aaronlubinsky/Romi_Lubinsky_Guinnane/images/diagrams/romi_dim_param.png

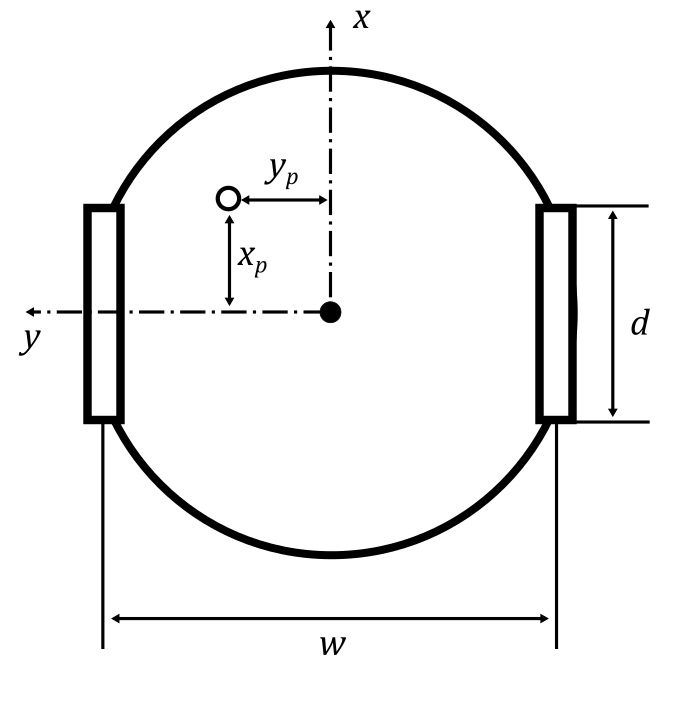
images/diagrams/romi_dim_param.png
