aaronlubinsky/Romi_Lubinsky_Guinnane/images/renders/RomiTop.jpg

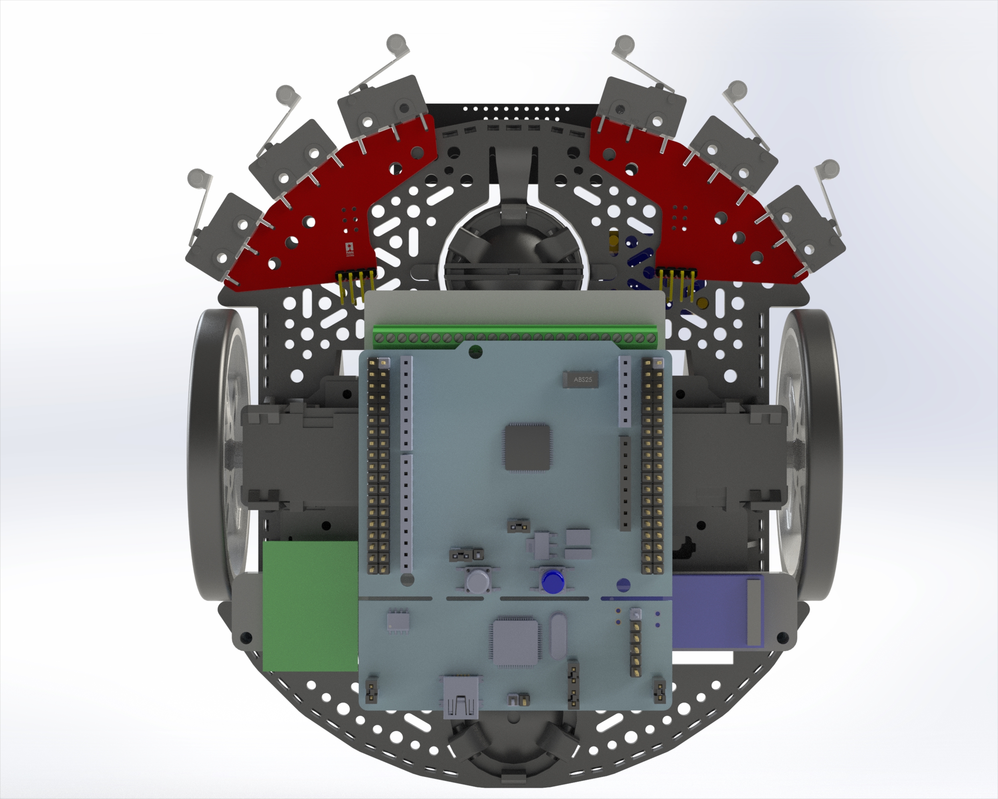
images/renders/RomiTop.jpg
