aaronlubinsky/Romi_Lubinsky_Guinnane/images/romi_pics/romi_back.jpg

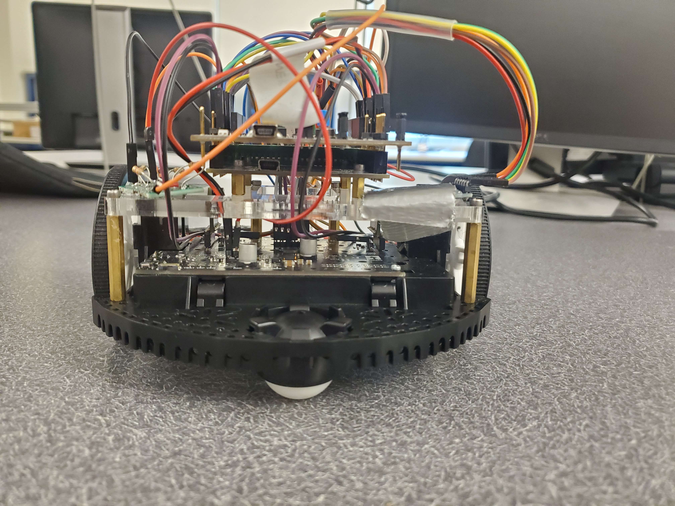
images/romi_pics/romi_back.jpg
