aaronlubinsky/Romi_Lubinsky_Guinnane/images/romi_pics/romi_bottom.jpg

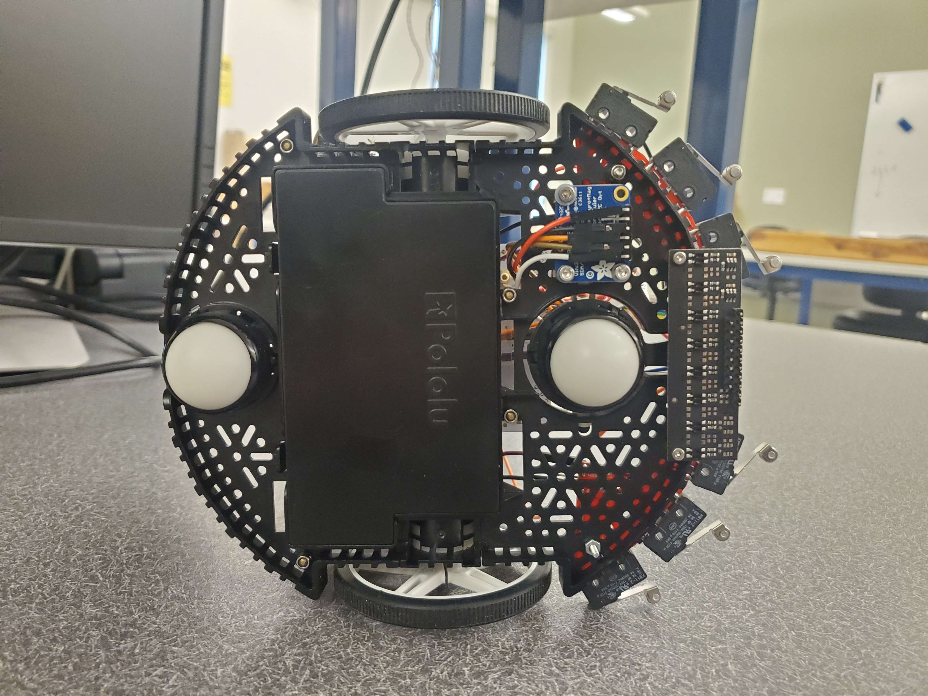
images/romi_pics/romi_bottom.jpg
