aaronlubinsky/Romi_Lubinsky_Guinnane/images/romi_pics/romi_top.jpg

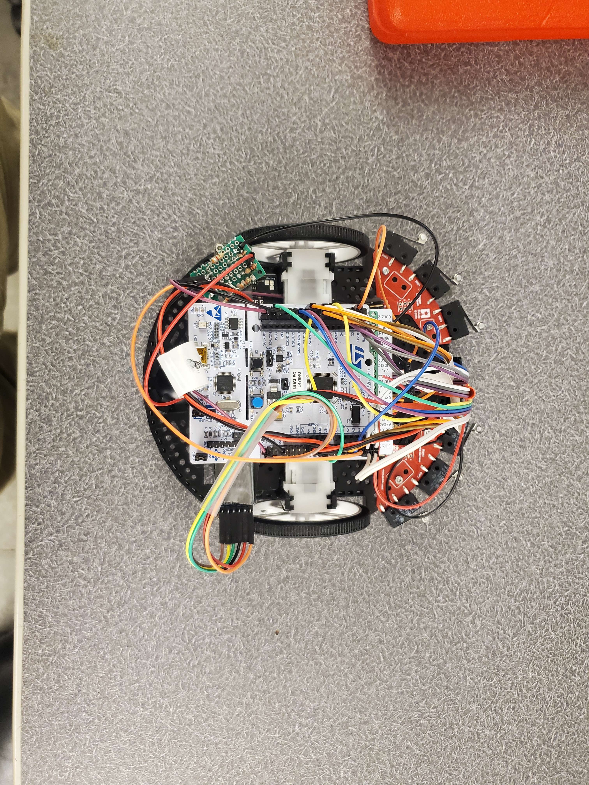
images/romi_pics/romi_top.jpg
